uutzinger/FoldingDisplay/assets/MiniView/V1/MiniView-Cover.dxf

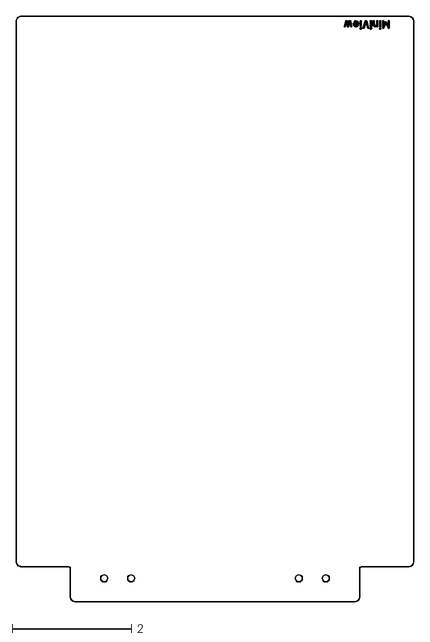
[picture p21: CAD file, 2025-04-06, an earlier design]
assets/MiniView/V1/MiniView-Cover.dxf
6.68 x 9.84
